ElectronicsTinkerer/D.R.U.M/module/cad/SIFAM - Slider Cap (black) .stp

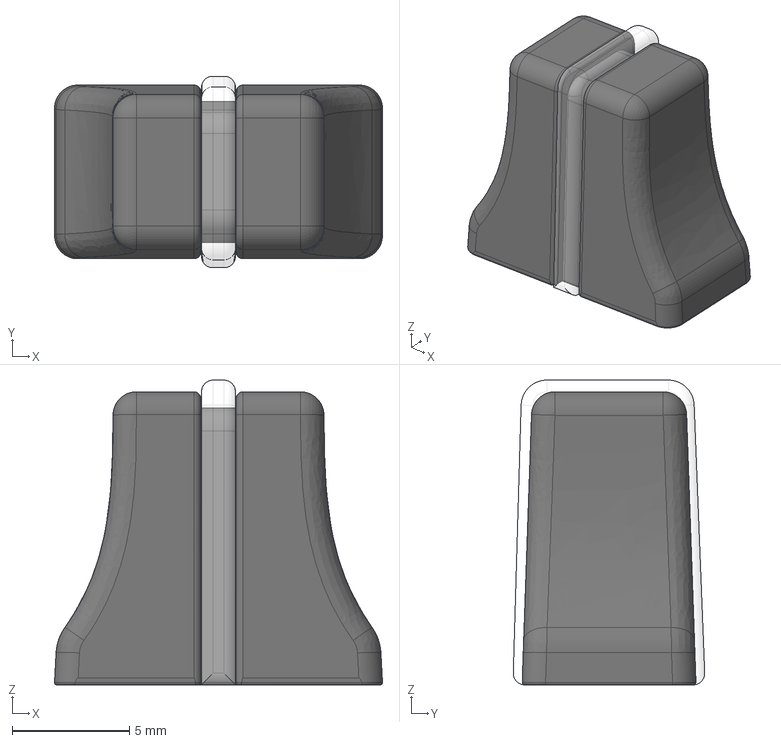
[picture p27: CAD file, 2022-11-13]
module/cad/SIFAM - Slider Cap (black) .stp
14.0 x 8.16 x 13.0 mm
