ElectronicsTinkerer/D.R.U.M/sequencer/cad/SeqBase.SLDPRT

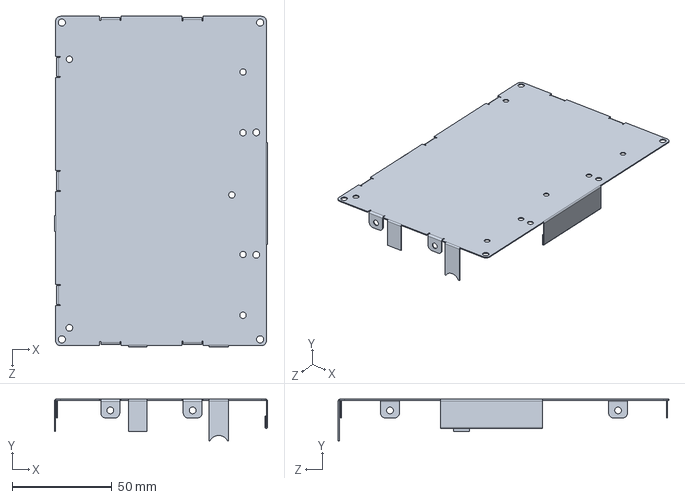
[picture p28: CAD file, 2022-11-21]
sequencer/cad/SeqBase.SLDPRT
106.7 x 20.8 x 165.6 mm
