ElectronicsTinkerer/D.R.U.M/sequencer/cad/RotaryEncoder.STEP

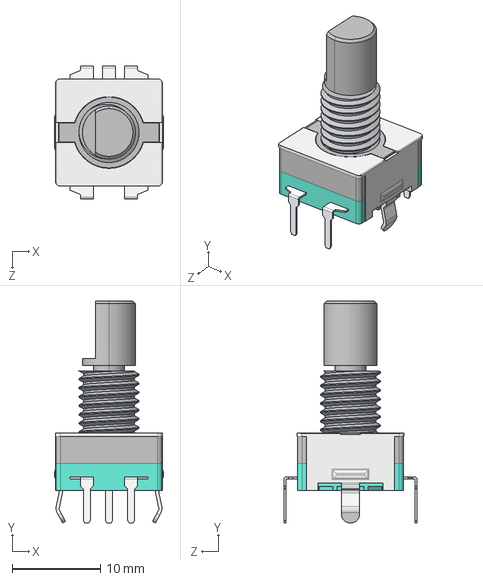
[picture p29: CAD file, 2022-11-13]
sequencer/cad/RotaryEncoder.STEP
12.3 x 25.1 x 15.0 mm
