ElectronicsTinkerer/D.R.U.M/module/cad/RV24AF-22-15K.step

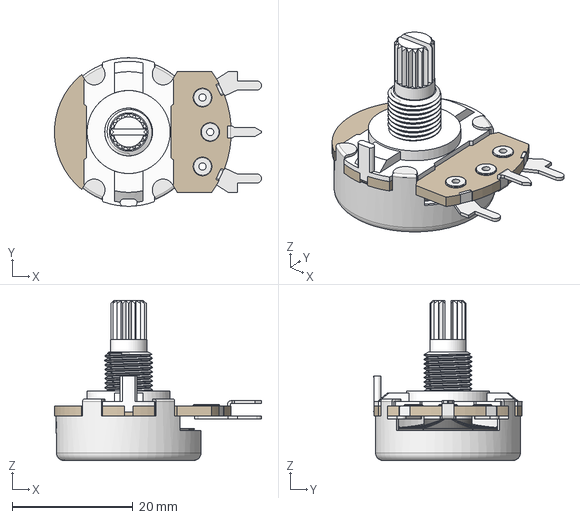
[picture p30: CAD file, 2022-11-13]
module/cad/RV24AF-22-15K.step
34.3 x 24.6 x 26.5 mm
