ElectronicsTinkerer/D.R.U.M/sequencer/cad/Adafruit 0.96in 128x64 OLED STEMMA QT.step

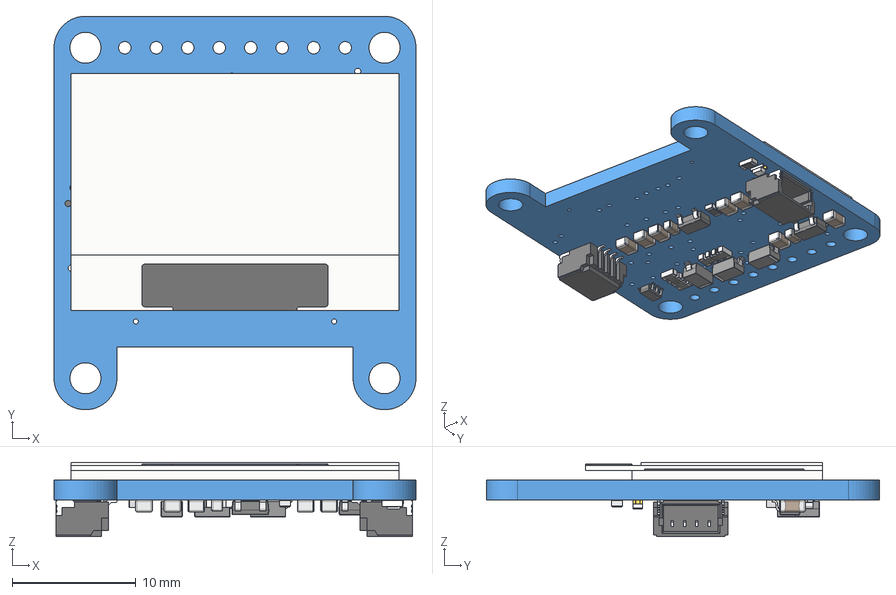
[picture p31: CAD file, 2022-11-13]
sequencer/cad/Adafruit 0.96in 128x64 OLED STEMMA QT.step
29.2 x 31.8 x 5.99 mm
Printed Circuit Board
Glass_Back
Circuit_Strip
Glass_Middle
Glass_Top
Tape_Strip
Cathode x 3
Anode x 3
Cathode Bar x 3
LED 0603 single color
qwicc x 2
SOT23-3
SOT23-5
SOT23-6
YC164_RESPACK x 2
RESC-0603 x 2
CAPC-0805-T0.95-BN x 7
CAPC-0603-T0.9-BN x 2
