ElectronicsTinkerer/D.R.U.M/sequencer/cad/Adafruit Trellis 3mm.stp

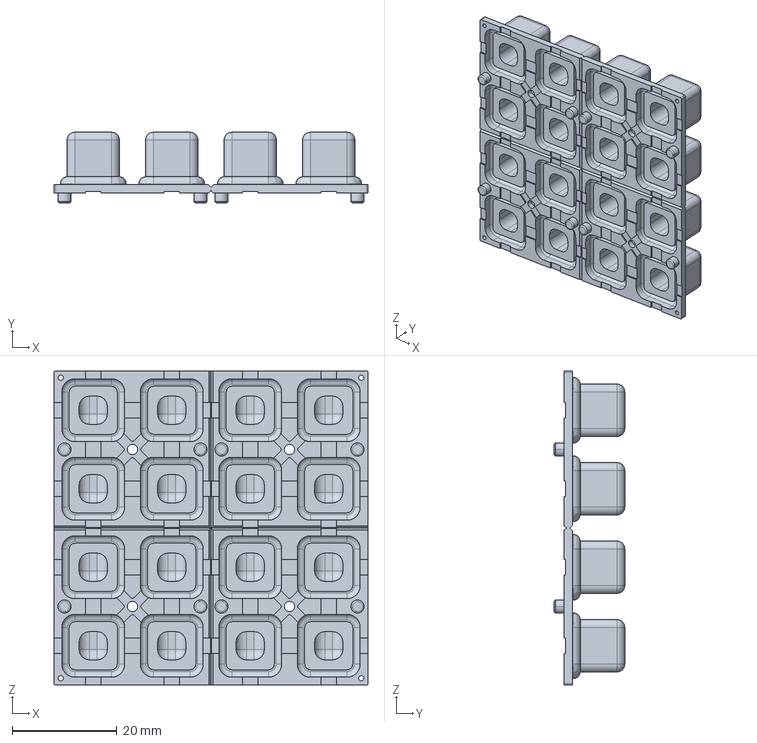
[picture p32: CAD file, 2022-11-13]
sequencer/cad/Adafruit Trellis 3mm.stp
60.0 x 13.5 x 60.0 mm
