ElectronicsTinkerer/D.R.U.M/sequencer/cad/Black - With Line (D-Shaft).stp

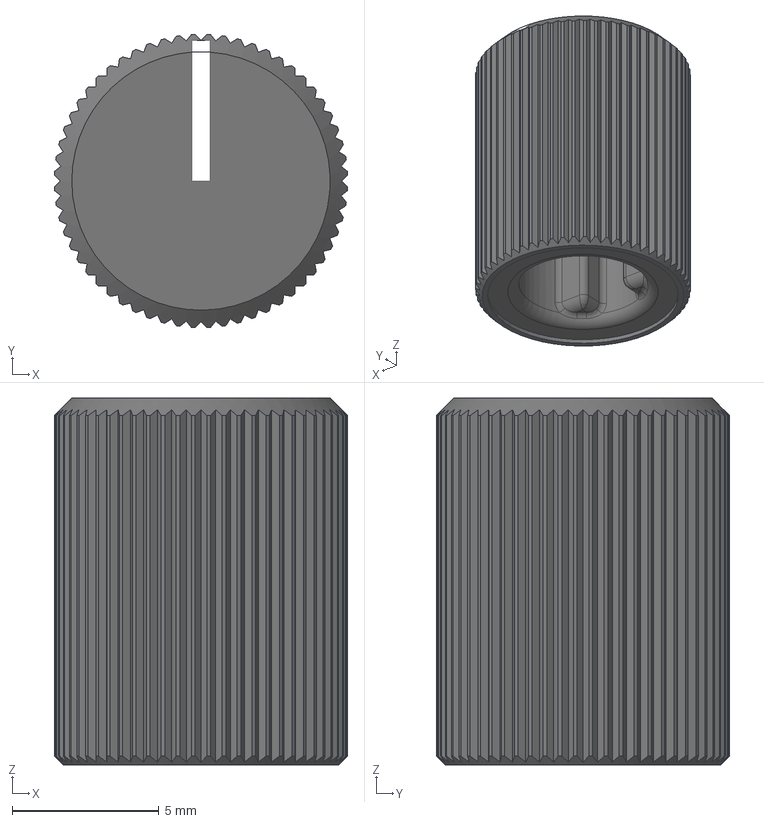
[picture p33: CAD file, 2022-11-13]
sequencer/cad/Black - With Line (D-Shaft).stp
9.99 x 9.99 x 12.5 mm
