ElectronicsTinkerer/D.R.U.M/sequencer/software/Adafruit_Lib/Arduino.h

#include "pico/stdlib.h"
#include <cstring>
#include <cstdlib>
#include <cstdio>

#ifndef _PSEUDO_ARDUINO_H
#define _PSEUDO_ARDUINO_H

typedef uint8_t byte;
typedef bool boolean;

#define OUTPUT GPIO_OUT
#define INPUT GPIO_IN
#define INPUT_PULLUP 233 // Hopefully not used???
#define INPUT_PULLDOWN 234

#define micros() ((unsigned long)get_absolute_time())
#define delay(t) (sleep_ms(t))
#define delayMicroseconds(t) (sleep_us(t))
#define min(x, y) (((x) < (y)) ? (x) : (y))
// #define pinMode(p, t) (gpio_set_dir((p), (t)))
// #define digitalWrite(p, s) (gpio_put((p), (s)))
// #define digitalRead(p) (gpio_get((p))

inline long map(long val, long i_min, long i_max, long o_min, long o_max)
{
    return ((val - i_min) * (o_max - o_min)) / (i_max - i_min);
}

char *ultoa(unsigned long value, char *string, int radix);
char *utoa(unsigned value, char *string, int radix);
char *ltoa(long value, char *string, int radix);
char *itoa(int value, char *string, int radix);
char *dtostrf(double val, signed char width, unsigned char prec, char *sout);

// class Print
// {
// public:
    // void pinMode(uint8_t, uint8_t);
    // bool digitalRead(uint8_t);
    /* empty? */
// };

#endif
